nejc-cc/hexaled/Photos/Project/Almost_done.jpg

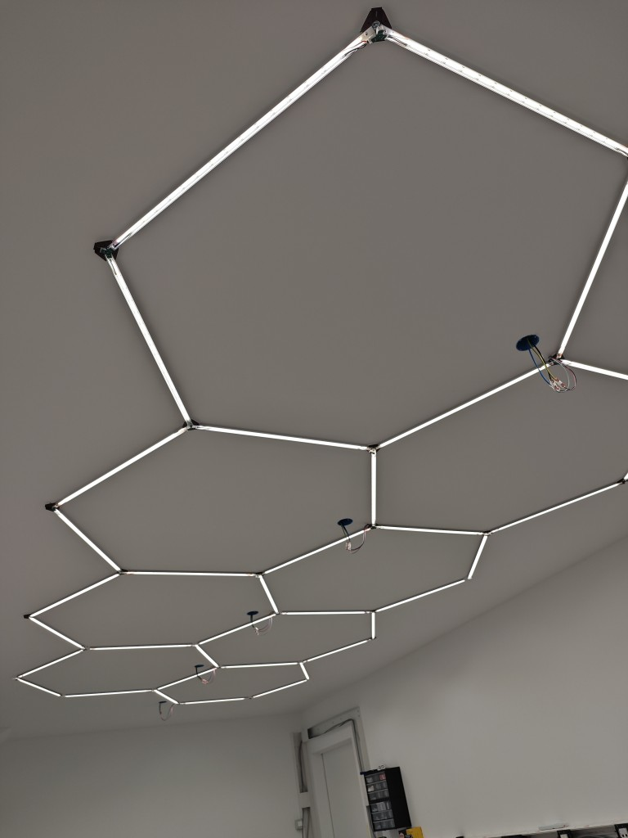
Photos/Project/Almost_done.jpg
