nejc-cc/hexaled/Photos/Project/Cable_cutting_jig_-_heatshrink_tube.jpg

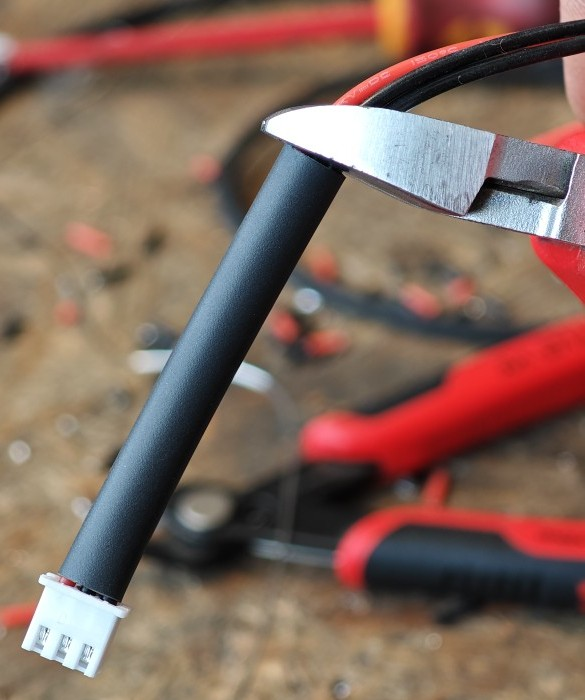
Photos/Project/Cable_cutting_jig_-_heatshrink_tube.jpg
