nejc-cc/hexaled/Photos/Project/Final_product.jpg

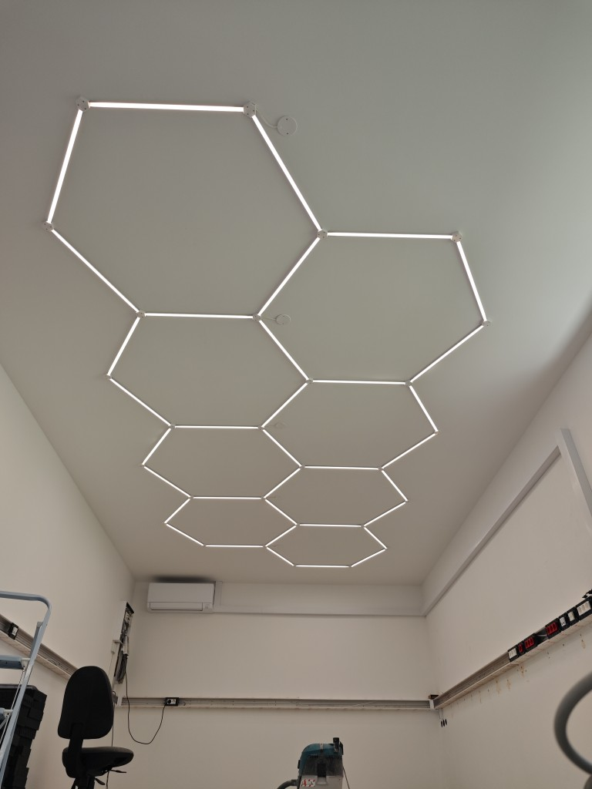
Photos/Project/Final_product.jpg
