nejc-cc/hexaled/Photos/Project/Juuust_a_little_bit.jpg

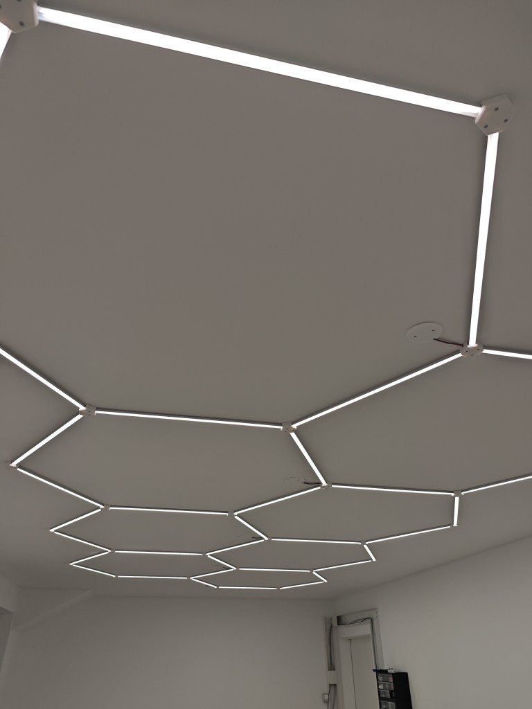
Photos/Project/Juuust_a_little_bit.jpg
