nejc-cc/hexaled/Photos/Project/When_you_run_out_of_filament.jpg

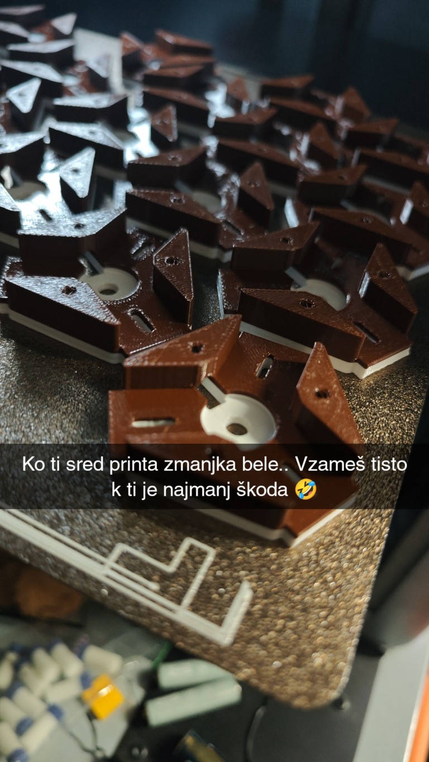
Photos/Project/When_you_run_out_of_filament.jpg
