nejc-cc/hexaled/Photos/Project/With_covers.jpg

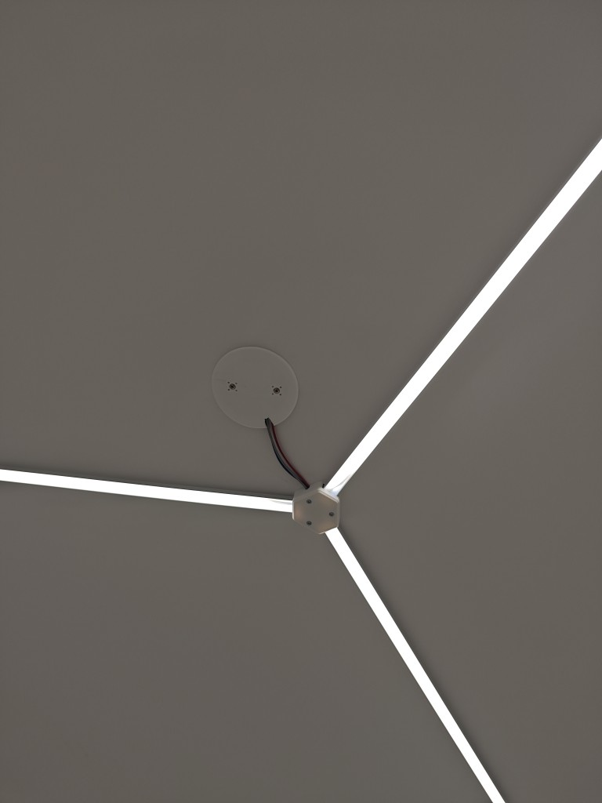
Photos/Project/With_covers.jpg
