nejc-cc/hexaled/Gerber and KiCad files/HexLED-dvojni/HexLED-dvojni.kicad_sch

## KiCad design Gerber and KiCad files/HexLED-dvojni/HexLED-dvojni.kicad_sch (2025-07-28)

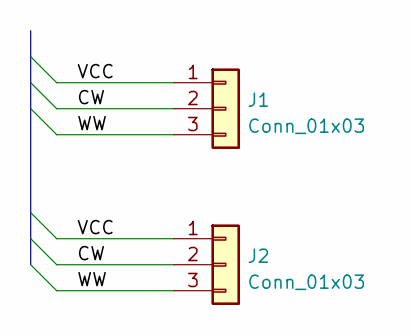
[picture p50: schematic HexLED-dvojni.kicad_sch]

Parts:
J1, J2: Conn_01x03; JST_XH_S3B-XH-A-1_1x03_P2.50mm_Horizontal

Connections:
CW: J1.2, J2.2
VCC: J1.1, J2.1
WW: J1.3, J2.3
